idorurez/mini_weather_monitor/sdcard/37_120x120.jpg

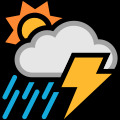
sdcard/37_120x120.jpg
