idorurez/mini_weather_monitor/sdcard/05_120x120.jpg

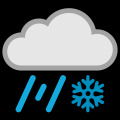
sdcard/05_120x120.jpg
