idorurez/mini_weather_monitor/sdcard/08_120x120.jpg

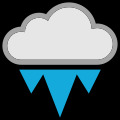
sdcard/08_120x120.jpg
