idorurez/mini_weather_monitor/sdcard/09_120x120.jpg

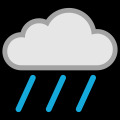
sdcard/09_120x120.jpg
