idorurez/mini_weather_monitor/sdcard/13_120x120.jpg

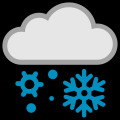
sdcard/13_120x120.jpg
