idorurez/mini_weather_monitor/sdcard/15_120x120.jpg

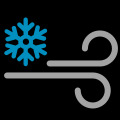
sdcard/15_120x120.jpg
