idorurez/mini_weather_monitor/sdcard/16_120x120.jpg

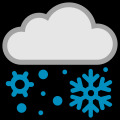
sdcard/16_120x120.jpg
