idorurez/mini_weather_monitor/sdcard/26_120x120.jpg

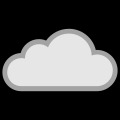
sdcard/26_120x120.jpg
