idorurez/mini_weather_monitor/sdcard/27_120x120.jpg

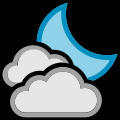
sdcard/27_120x120.jpg
