idorurez/mini_weather_monitor/sdcard/28_120x120.jpg

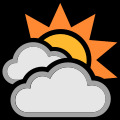
sdcard/28_120x120.jpg
