idorurez/mini_weather_monitor/sdcard/29_120x120.jpg

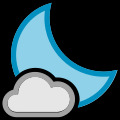
sdcard/29_120x120.jpg
