idorurez/mini_weather_monitor/sdcard/30_120x120.jpg

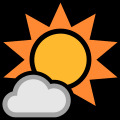
sdcard/30_120x120.jpg
