idorurez/mini_weather_monitor/sdcard/31_120x120.jpg

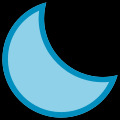
sdcard/31_120x120.jpg
