idorurez/mini_weather_monitor/sdcard/32_120x120.jpg

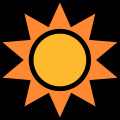
sdcard/32_120x120.jpg
