idorurez/mini_weather_monitor/sdcard/41_120x120.jpg

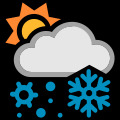
sdcard/41_120x120.jpg
