idorurez/mini_weather_monitor/sdcard/44_120x120.jpg

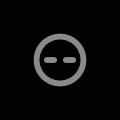
sdcard/44_120x120.jpg
