idorurez/mini_weather_monitor/sdcard/45_120x120.jpg

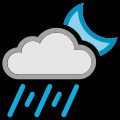
sdcard/45_120x120.jpg
