idorurez/mini_weather_monitor/sdcard/46_120x120.jpg

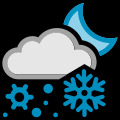
sdcard/46_120x120.jpg
